lordzurp/Cam87-box/#0_DataSheets/ICX453AQ_PinOut.jpg

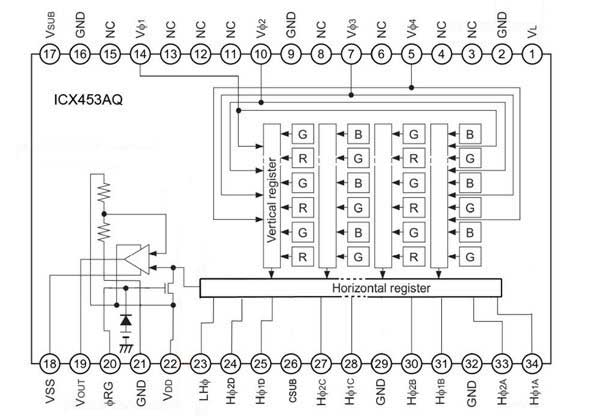
#0_DataSheets/ICX453AQ_PinOut.jpg
