lordzurp/Cam87-box/#1_Power_board/Cam87-box 1.2.1 - Power board - 2_3D-view.png

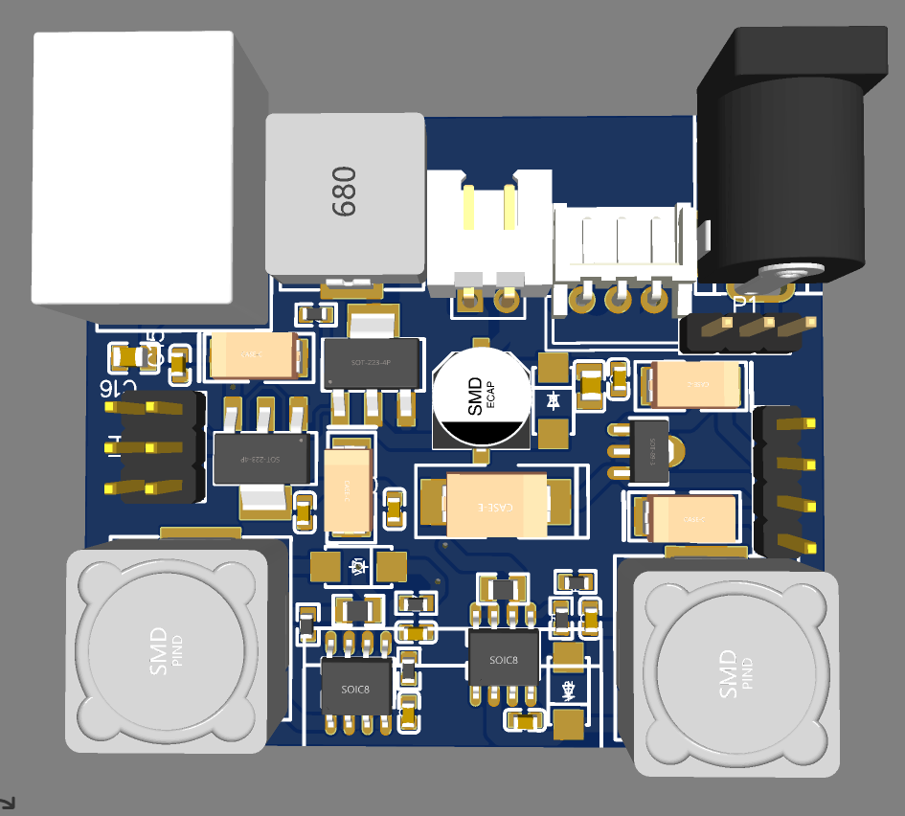
#1_Power_board/Cam87-box 1.2.1 - Power board - 2_3D-view.png
