lordzurp/Cam87-box/#2_Logic_board/Cam87-box 1.2 - Logic board - 2_3D-view.png

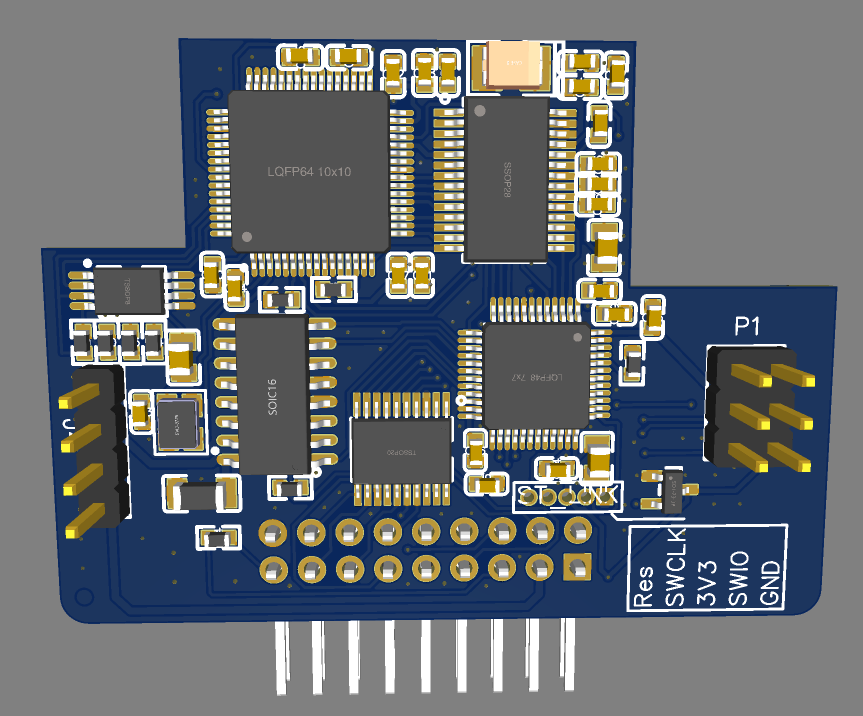
#2_Logic_board/Cam87-box 1.2 - Logic board - 2_3D-view.png
