lordzurp/Cam87-box/#3_Sensor_board/Cam87-box 1.2 - Sensor board - 2_2D_view.png

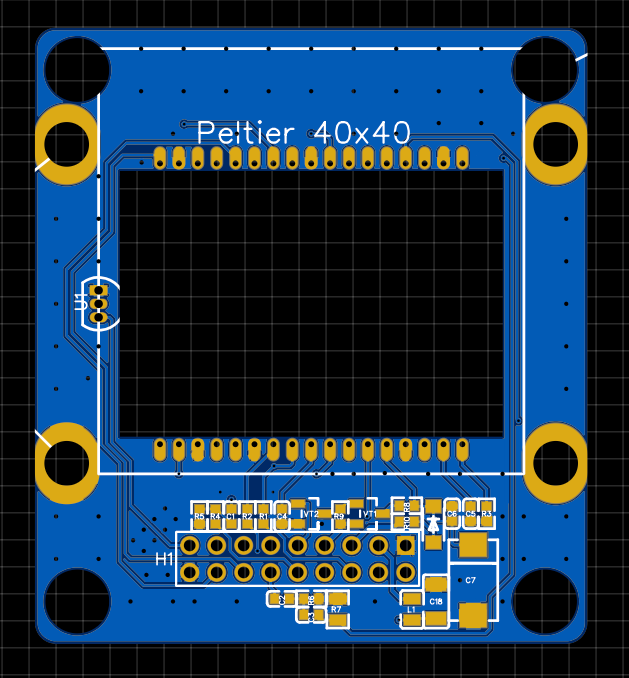
#3_Sensor_board/Cam87-box 1.2 - Sensor board - 2_2D_view.png
